seb1010/SolderingIronController/images/IMG_4085.JPG

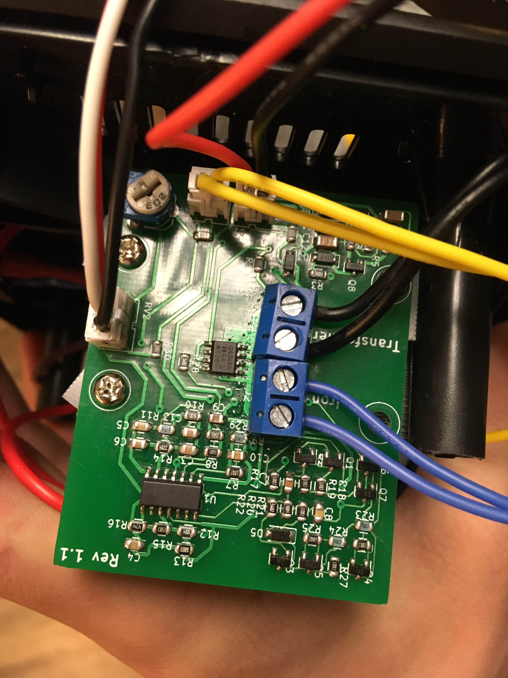
images/IMG_4085.JPG
